emukidid/SNES_APU_SD/SNES_APU_SD/LCD.cpp

#if (defined(__AVR_ATmega2560__) || defined(__AVR_ATmega1280__))
#include "LCD.h"

#include <stdio.h>
#include <string.h>
#include <inttypes.h>
#include "Arduino.h"

// When the display powers up, it is configured as follows:
//
// 1. Display clear
// 2. Function set: 
//    DL = 1; 8-bit interface data 
//    N = 0; 1-line display 
//    F = 0; 5x8 dot character font 
// 3. Display on/off control: 
//    D = 0; Display off 
//    C = 0; Cursor off 
//    B = 0; Blinking off 
// 4. Entry mode set: 
//    I/D = 1; Increment by 1 
//    S = 0; No shift 
//
// Note, however, that resetting the Arduino doesn't reset the LCD, so we
// can't assume that its in that state when a sketch starts (and the
// LiquidCrystal constructor is called).

LiquidCrystal::LiquidCrystal()
{
  init();
}

void LiquidCrystal::init()
{
  DDRF = 0xFF;
  DDRH = 0xFF;
  DDRK = 0x07;
  _displayfunction = LCD_8BITMODE | LCD_1LINE | LCD_5x8DOTS;
  
  begin(16, 2);  
}

void LiquidCrystal::begin(uint8_t cols, uint8_t lines, uint8_t dotsize) {
  if (lines > 1) {
    _displayfunction |= LCD_2LINE;
  }
  _numlines = lines;

  setRowOffsets(0x00, 0x40, 0x00 + cols, 0x40 + cols);  

  // for some 1 line displays you can select a 10 pixel high font
  if ((dotsize != LCD_5x8DOTS) && (lines == 1)) {
    _displayfunction |= LCD_5x10DOTS;
  }

  // SEE PAGE 45/46 FOR INITIALIZATION SPECIFICATION!
  // according to datasheet, we need at least 40ms after power rises above 2.7V
  // before sending commands. Arduino can turn on way before 4.5V so we'll wait 50
  delayMicroseconds(50000); 
  // Now we pull both RS and R/W low to begin commands
  PORTK &= ~LCD_RS;
  PORTK &= ~LCD_E;
  PORTK &= ~LCD_RW;
  
  //put the LCD into 4 bit or 8 bit mode

  // this is according to the hitachi HD44780 datasheet
  // page 45 figure 23

  // Send function set command sequence
  command(LCD_FUNCTIONSET | _displayfunction);
  delayMicroseconds(4500);  // wait more than 4.1ms

  // second try
  command(LCD_FUNCTIONSET | _displayfunction);
  delayMicroseconds(150);

  // third go
  command(LCD_FUNCTIONSET | _displayfunction);

  // finally, set # lines, font size, etc.
  command(LCD_FUNCTIONSET | _displayfunction);  

  // turn the display on with no cursor or blinking default
  _displaycontrol = LCD_DISPLAYON | LCD_CURSOROFF | LCD_BLINKOFF;  
  display();

  // clear it off
  clear();

  // Initialize to default text direction (for romance languages)
  _displaymode = LCD_ENTRYLEFT | LCD_ENTRYSHIFTDECREMENT;
  // set the entry mode
  command(LCD_ENTRYMODESET | _displaymode);

}

/*
   in some 16x4 LCD when line 3 and 4 are not placed correctly you may try:
     setRowOffsets(0x00, 0x40, 0x14, 0x54)
   or
     setRowOffsets(0x00, 0x40, 0x10, 0x50)
 */
void LiquidCrystal::setRowOffsets(int row0, int row1, int row2, int row3)
{
  _row_offsets[0] = row0;
  _row_offsets[1] = row1;
  _row_offsets[2] = row2;
  _row_offsets[3] = row3;
}

/********** high level commands, for the user! */
void LiquidCrystal::clear()
{
  command(LCD_CLEARDISPLAY);  // clear display, set cursor position to zero
  delayMicroseconds(2000);  // this command takes a long time!
}

void LiquidCrystal::home()
{
  command(LCD_RETURNHOME);  // set cursor position to zero
  delayMicroseconds(2000);  // this command takes a long time!
}

void LiquidCrystal::setCursor(uint8_t col, uint8_t row)
{
  const size_t max_lines = sizeof(_row_offsets) / sizeof(*_row_offsets);
  if ( row >= max_lines ) {
    row = max_lines - 1;    // we count rows starting w/0
  }
  if ( row >= _numlines ) {
    row = _numlines - 1;    // we count rows starting w/0
  }
  
  command(LCD_SETDDRAMADDR | (col + _row_offsets[row]));
}

// Turn the display on/off (quickly)
void LiquidCrystal::noDisplay() {
  _displaycontrol &= ~LCD_DISPLAYON;
  command(LCD_DISPLAYCONTROL | _displaycontrol);
}
void LiquidCrystal::display() {
  _displaycontrol |= LCD_DISPLAYON;
  command(LCD_DISPLAYCONTROL | _displaycontrol);
}

// Turns the underline cursor on/off
void LiquidCrystal::noCursor() {
  _displaycontrol &= ~LCD_CURSORON;
  command(LCD_DISPLAYCONTROL | _displaycontrol);
}
void LiquidCrystal::cursor() {
  _displaycontrol |= LCD_CURSORON;
  command(LCD_DISPLAYCONTROL | _displaycontrol);
}

// Turn on and off the blinking cursor
void LiquidCrystal::noBlink() {
  _displaycontrol &= ~LCD_BLINKON;
  command(LCD_DISPLAYCONTROL | _displaycontrol);
}
void LiquidCrystal::blink() {
  _displaycontrol |= LCD_BLINKON;
  command(LCD_DISPLAYCONTROL | _displaycontrol);
}

// These commands scroll the display without changing the RAM
void LiquidCrystal::scrollDisplayLeft(void) {
  command(LCD_CURSORSHIFT | LCD_DISPLAYMOVE | LCD_MOVELEFT);
}
void LiquidCrystal::scrollDisplayRight(void) {
  command(LCD_CURSORSHIFT | LCD_DISPLAYMOVE | LCD_MOVERIGHT);
}

// This is for text that flows Left to Right
void LiquidCrystal::leftToRight(void) {
  _displaymode |= LCD_ENTRYLEFT;
  command(LCD_ENTRYMODESET | _displaymode);
}

// This is for text that flows Right to Left
void LiquidCrystal::rightToLeft(void) {
  _displaymode &= ~LCD_ENTRYLEFT;
  command(LCD_ENTRYMODESET | _displaymode);
}

// This will 'right justify' text from the cursor
void LiquidCrystal::autoscroll(void) {
  _displaymode |= LCD_ENTRYSHIFTINCREMENT;
  command(LCD_ENTRYMODESET | _displaymode);
}

// This will 'left justify' text from the cursor
void LiquidCrystal::noAutoscroll(void) {
  _displaymode &= ~LCD_ENTRYSHIFTINCREMENT;
  command(LCD_ENTRYMODESET | _displaymode);
}

// Allows us to fill the first 8 CGRAM locations
// with custom characters
void LiquidCrystal::createChar(uint8_t location, uint8_t charmap[]) {
  location &= 0x7; // we only have 8 locations 0-7
  command(LCD_SETCGRAMADDR | (location << 3));
  for (int i=0; i<8; i++) {
    write(charmap[i]);
  }
}

/*********** mid level commands, for sending data/cmds */

inline void LiquidCrystal::command(uint8_t value) {
  send(value, LOW);
}

inline size_t LiquidCrystal::write(uint8_t value) {
  send(value, HIGH);
  return 1; // assume sucess
}

/************ low level data pushing commands **********/

// write either command or data, with automatic 4/8-bit selection
void LiquidCrystal::send(uint8_t value, uint8_t mode) {
  if(mode==HIGH)
    PORTK |= LCD_RS;
  else
    PORTK &= ~LCD_RS;

  // if there is a RW pin indicated, set it low to Write
  PORTK &= ~LCD_RW;
  
  write8bits(value);
}

void LiquidCrystal::pulseEnable(void) {
  PORTK &= ~LCD_E;
  delayMicroseconds(1);
  PORTK |= LCD_E;
  delayMicroseconds(1);    // enable pulse must be >450ns
  PORTK &= ~LCD_E;
  delayMicroseconds(100);   // commands need > 37us to settle
}

const uint8_t lcd_reverse_bits[256] PROGMEM = 
{
  0x00, 0x80, 0x40, 0xC0, 0x20, 0xA0, 0x60, 0xE0, 0x10, 0x90, 0x50, 0xD0, 0x30, 0xB0, 0x70, 0xF0, 
  0x08, 0x88, 0x48, 0xC8, 0x28, 0xA8, 0x68, 0xE8, 0x18, 0x98, 0x58, 0xD8, 0x38, 0xB8, 0x78, 0xF8, 
  0x04, 0x84, 0x44, 0xC4, 0x24, 0xA4, 0x64, 0xE4, 0x14, 0x94, 0x54, 0xD4, 0x34, 0xB4, 0x74, 0xF4, 
  0x0C, 0x8C, 0x4C, 0xCC, 0x2C, 0xAC, 0x6C, 0xEC, 0x1C, 0x9C, 0x5C, 0xDC, 0x3C, 0xBC, 0x7C, 0xFC, 
  0x02, 0x82, 0x42, 0xC2, 0x22, 0xA2, 0x62, 0xE2, 0x12, 0x92, 0x52, 0xD2, 0x32, 0xB2, 0x72, 0xF2, 
  0x0A, 0x8A, 0x4A, 0xCA, 0x2A, 0xAA, 0x6A, 0xEA, 0x1A, 0x9A, 0x5A, 0xDA, 0x3A, 0xBA, 0x7A, 0xFA, 
  0x06, 0x86, 0x46, 0xC6, 0x26, 0xA6, 0x66, 0xE6, 0x16, 0x96, 0x56, 0xD6, 0x36, 0xB6, 0x76, 0xF6, 
  0x0E, 0x8E, 0x4E, 0xCE, 0x2E, 0xAE, 0x6E, 0xEE, 0x1E, 0x9E, 0x5E, 0xDE, 0x3E, 0xBE, 0x7E, 0xFE, 
  0x01, 0x81, 0x41, 0xC1, 0x21, 0xA1, 0x61, 0xE1, 0x11, 0x91, 0x51, 0xD1, 0x31, 0xB1, 0x71, 0xF1, 
  0x09, 0x89, 0x49, 0xC9, 0x29, 0xA9, 0x69, 0xE9, 0x19, 0x99, 0x59, 0xD9, 0x39, 0xB9, 0x79, 0xF9, 
  0x05, 0x85, 0x45, 0xC5, 0x25, 0xA5, 0x65, 0xE5, 0x15, 0x95, 0x55, 0xD5, 0x35, 0xB5, 0x75, 0xF5, 
  0x0D, 0x8D, 0x4D, 0xCD, 0x2D, 0xAD, 0x6D, 0xED, 0x1D, 0x9D, 0x5D, 0xDD, 0x3D, 0xBD, 0x7D, 0xFD, 
  0x03, 0x83, 0x43, 0xC3, 0x23, 0xA3, 0x63, 0xE3, 0x13, 0x93, 0x53, 0xD3, 0x33, 0xB3, 0x73, 0xF3, 
  0x0B, 0x8B, 0x4B, 0xCB, 0x2B, 0xAB, 0x6B, 0xEB, 0x1B, 0x9B, 0x5B, 0xDB, 0x3B, 0xBB, 0x7B, 0xFB, 
  0x07, 0x87, 0x47, 0xC7, 0x27, 0xA7, 0x67, 0xE7, 0x17, 0x97, 0x57, 0xD7, 0x37, 0xB7, 0x77, 0xF7, 
  0x0F, 0x8F, 0x4F, 0xCF, 0x2F, 0xAF, 0x6F, 0xEF, 0x1F, 0x9F, 0x5F, 0xDF, 0x3F, 0xBF, 0x7F, 0xFF, 
};

void LiquidCrystal::write8bits(uint8_t value) {
  DDRF = 0xFF;
  PORTF = pgm_read_byte_near(lcd_reverse_bits + value);
  DDRH = 0xFF;
  PORTH = value;
  pulseEnable();
}
#endif
