emukidid/SNES_APU_SD/SNES_APU_SD/APU.h

#ifndef APU_h
#define APU_h

#define EX_SRAM(address) _SFR_MEM8(address+0x8000)

#define APU_TYPE_LEGACY 0
#define APU_TYPE_XMEM 1

#include <inttypes.h>

#if (defined(__AVR_ATmega2560__) || defined(__AVR_ATmega1280__))
  #define RESET_PIN_0 54
  #define RESET_PIN_1 43
  #define SRAM_PIN_0 38
  #define SRAM_PIN_1 42
  #define ARDUINO_MEGA
  
  #define LEFT 0
  #define UP 1
  #define DOWN 2
  #define RIGHT 3
  #define SELECT 4
#else
  #define RESET_PIN 14
#endif

class APU
{
public:
  APU();
  APU(uint8_t type);
  void init(uint8_t type);
  uint8_t read(uint8_t address);
  uint8_t read_xmem(uint8_t *addr);
  void write(uint8_t address, uint8_t data);
  void write_xmem(uint8_t *addr, uint8_t data);
  void reset();
private:
  uint8_t read_arduino(uint8_t address);
  uint8_t read_arduino_mega(uint8_t address);
  uint8_t read_arduino_mega_xmem(uint8_t address);
  void write_arduino(uint8_t address, uint8_t data);
  void write_arduino_mega(uint8_t address, uint8_t data);
  void write_arduino_mega_xmem(uint8_t address, uint8_t data);
  void reset_arduino();
  void reset_arduino_mega();
  void reset_arduino_mega_xmem();
  void init_mega();
  int init_mega_xmem();
  uint8_t mega_type;
  
  
};

#endif
